Magister54/opengauge/mpguino/mpguino.png

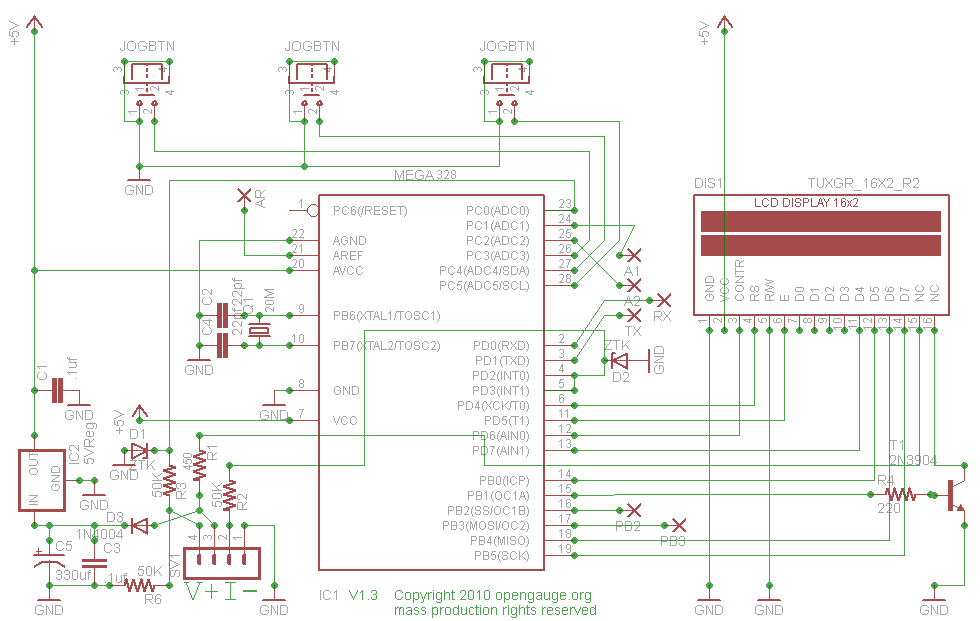
mpguino/mpguino.png
